fontysrobotics/cross_robot_localization_with_UWB_COLAB/PhysicalSystem/3D_Models/Downloaded/5mm-led-grommit-1.snapshot.1/5mm LED GROMMIT.jpg

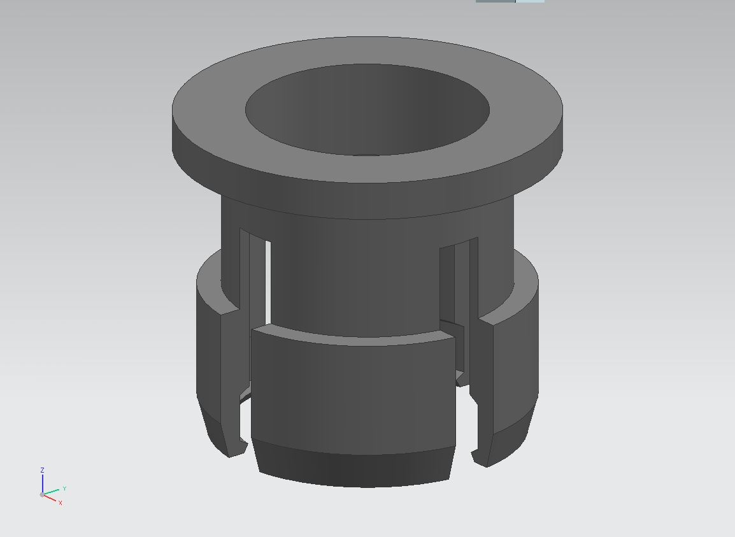
PhysicalSystem/3D_Models/Downloaded/5mm-led-grommit-1.snapshot.1/5mm LED GROMMIT.jpg
