fontysrobotics/cross_robot_localization_with_UWB_COLAB/PhysicalSystem/3D_Models/Downloaded/30mm-dc-fan-1.snapshot.6/30 fan decal.png

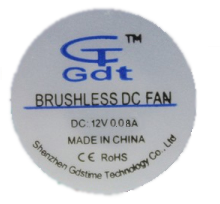
PhysicalSystem/3D_Models/Downloaded/30mm-dc-fan-1.snapshot.6/30 fan decal.png
