fontysrobotics/cross_robot_localization_with_UWB_COLAB/PhysicalSystem/3D_Models/Downloaded/30mm-dc-fan-1.snapshot.6/30mm fan.jpg

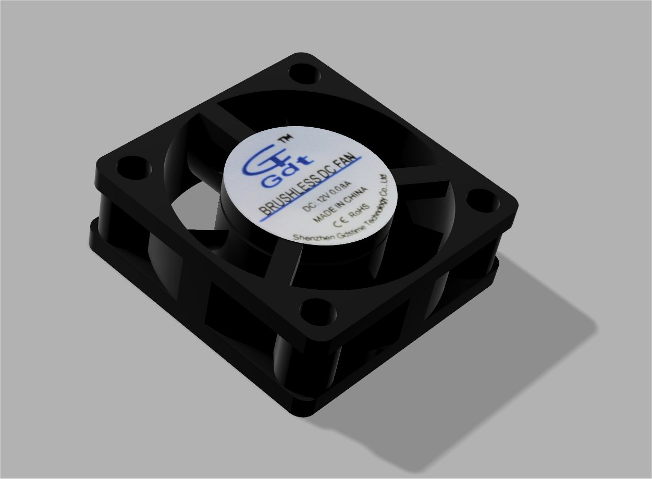
PhysicalSystem/3D_Models/Downloaded/30mm-dc-fan-1.snapshot.6/30mm fan.jpg
