fontysrobotics/cross_robot_localization_with_UWB_COLAB/PhysicalSystem/3D_Models/Downloaded/AAA battery holder/ScreenShot 2020-10-25 16.12.19.png

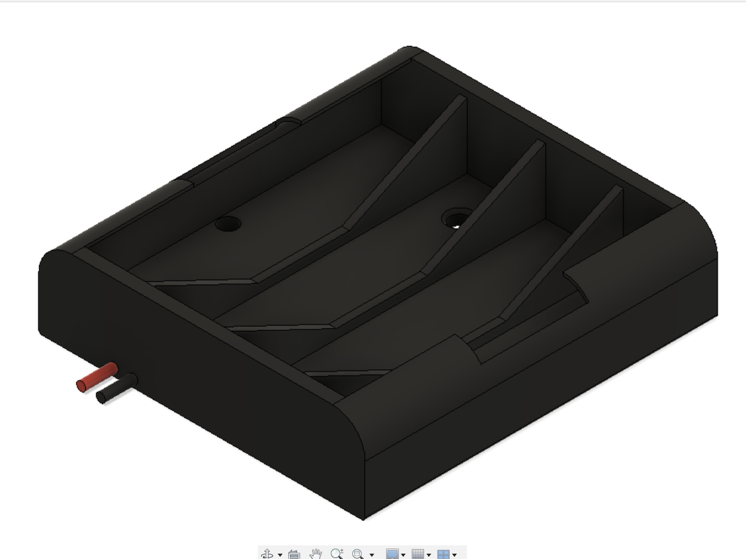
PhysicalSystem/3D_Models/Downloaded/AAA battery holder/ScreenShot 2020-10-25 16.12.19.png
