fontysrobotics/cross_robot_localization_with_UWB_COLAB/PhysicalSystem/3D_Models/Downloaded/led-5mm-2.snapshot.16/Renderings/untitled.57.jpg

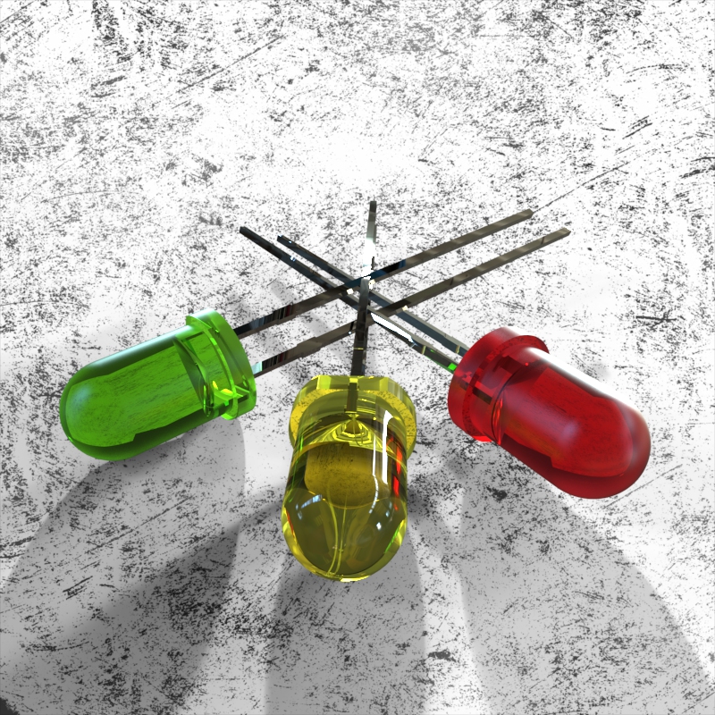
PhysicalSystem/3D_Models/Downloaded/led-5mm-2.snapshot.16/Renderings/untitled.57.jpg
