fontysrobotics/cross_robot_localization_with_UWB_COLAB/PhysicalSystem/3D_Models/Downloaded/m12-cable-gland-1.snapshot.1/gland_m12.jpg

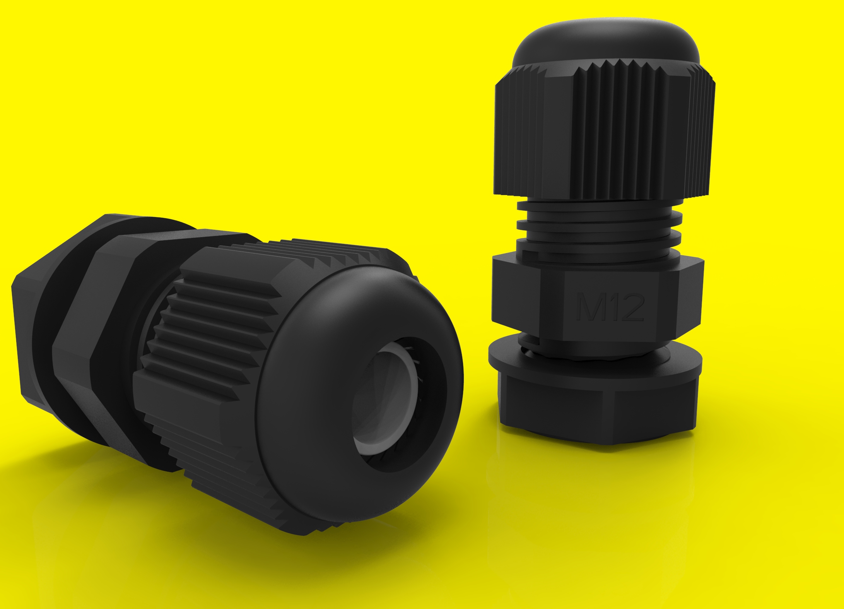
PhysicalSystem/3D_Models/Downloaded/m12-cable-gland-1.snapshot.1/gland_m12.jpg
