fontysrobotics/cross_robot_localization_with_UWB_COLAB/PhysicalSystem/3D_Models/Downloaded/small-power-switches-rocker-type-10-5x15mm-1.snapshot.7/KCD1-11-2P-Off.png

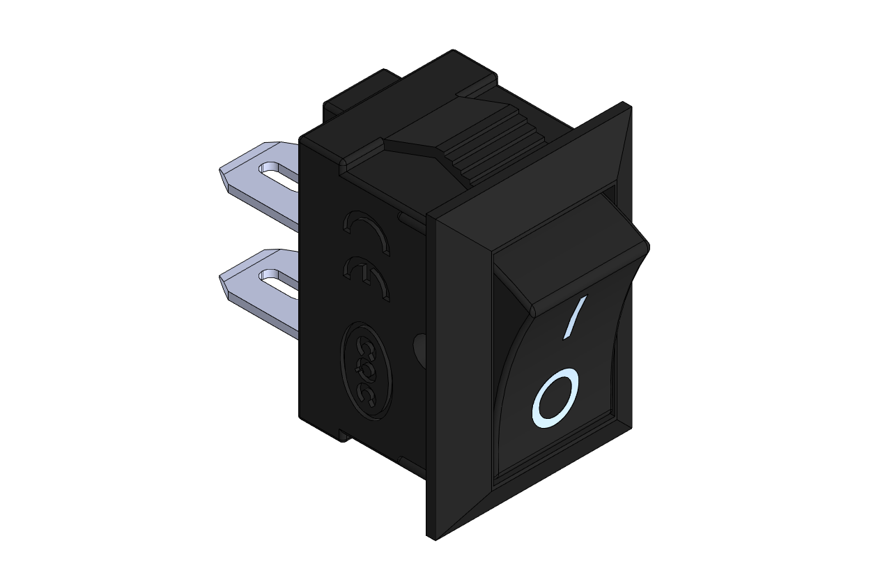
PhysicalSystem/3D_Models/Downloaded/small-power-switches-rocker-type-10-5x15mm-1.snapshot.7/KCD1-11-2P-Off.png
