fontysrobotics/cross_robot_localization_with_UWB_COLAB/Wiki_Images/AGVinfoAutonomy.PNG

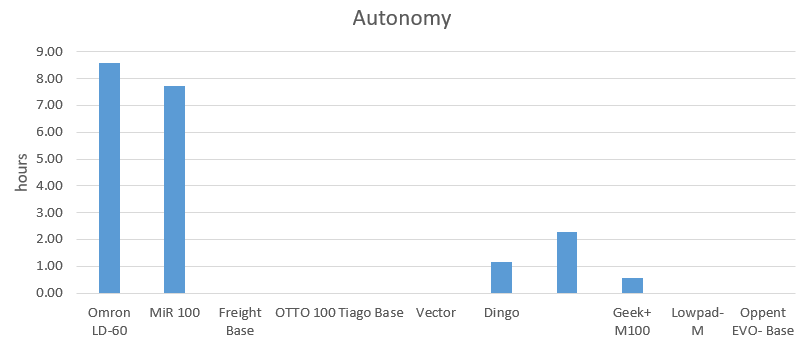
Wiki_Images/AGVinfoAutonomy.PNG
