fontysrobotics/cross_robot_localization_with_UWB_COLAB/Wiki_Images/AGVinfoBatteryTable.PNG

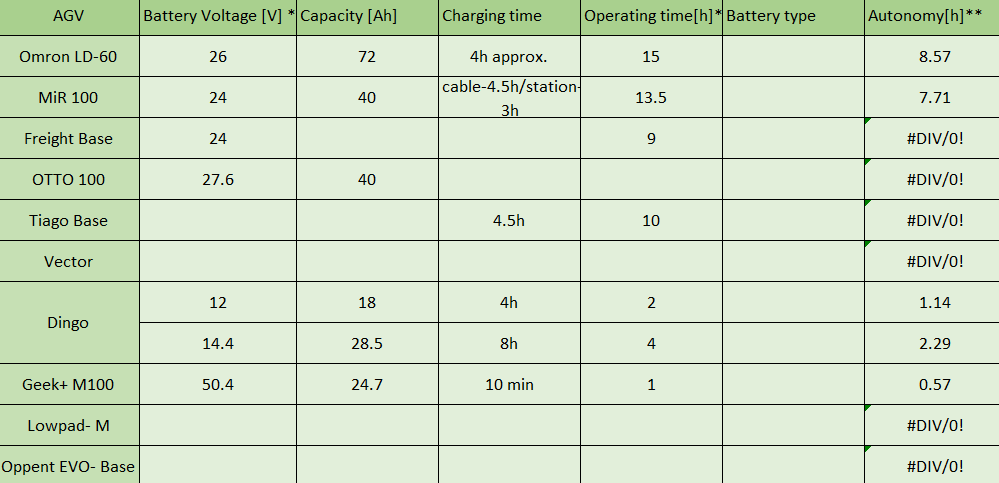
Wiki_Images/AGVinfoBatteryTable.PNG
