fontysrobotics/cross_robot_localization_with_UWB_COLAB/Wiki_Images/AGVinfoMaxLoad.PNG

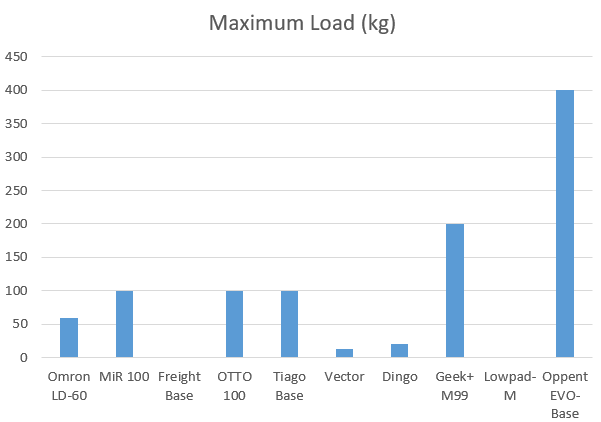
Wiki_Images/AGVinfoMaxLoad.PNG
