fontysrobotics/cross_robot_localization_with_UWB_COLAB/Wiki_Images/AGVinfoPlacement.PNG

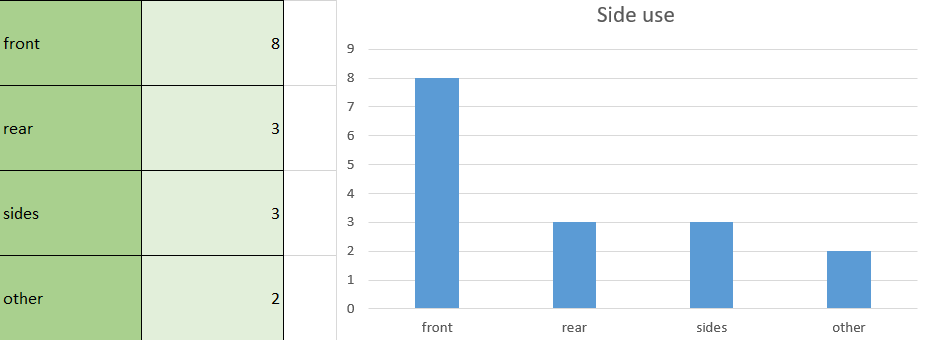
Wiki_Images/AGVinfoPlacement.PNG
