fontysrobotics/cross_robot_localization_with_UWB_COLAB/Wiki_Images/AGVinfoVolume.PNG

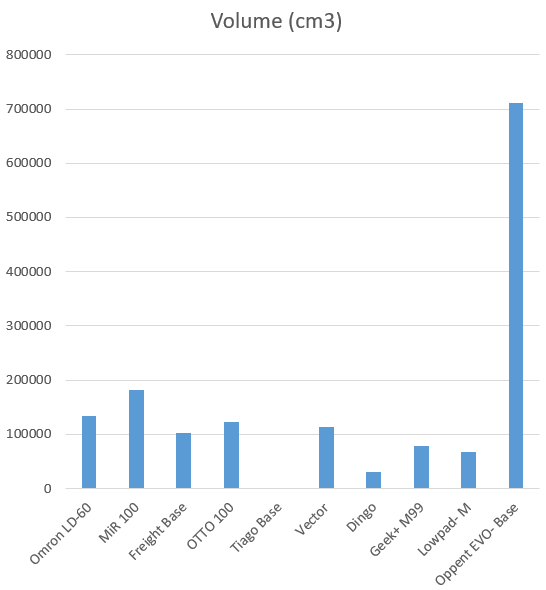
Wiki_Images/AGVinfoVolume.PNG
