fontysrobotics/cross_robot_localization_with_UWB_COLAB/Wiki_Images/AGVinfoWeight.PNG

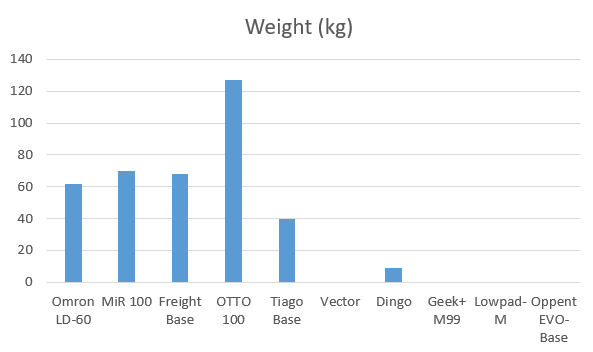
Wiki_Images/AGVinfoWeight.PNG
