fontysrobotics/cross_robot_localization_with_UWB_COLAB/Wiki_Images/CoLAB Housing PCB.png

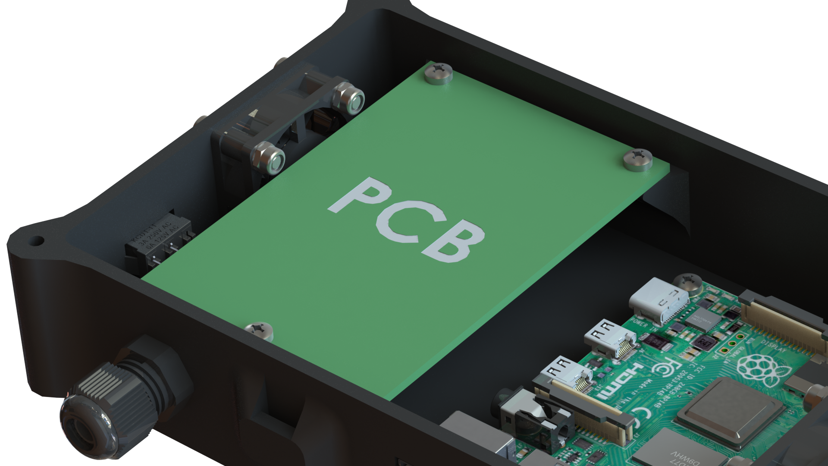
Wiki_Images/CoLAB Housing PCB.png
