fontysrobotics/cross_robot_localization_with_UWB_COLAB/Wiki_Images/CoLAB Housing Switch.png

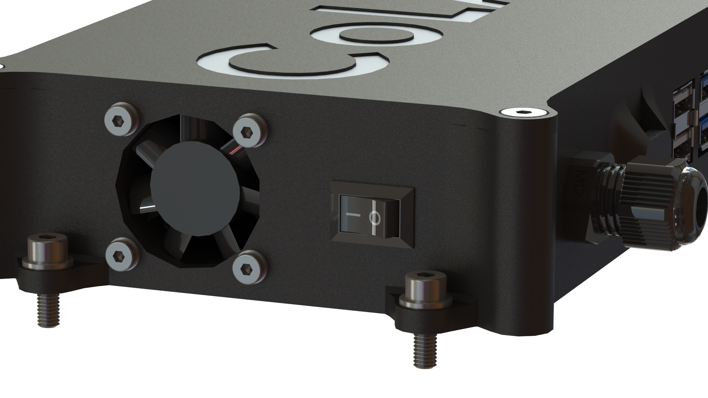
Wiki_Images/CoLAB Housing Switch.png
