fontysrobotics/cross_robot_localization_with_UWB_COLAB/Wiki_Images/connection_diagram_LM2596.JPG

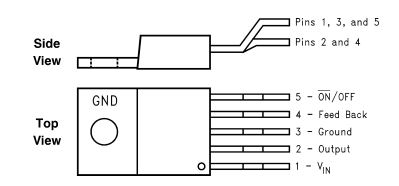
Wiki_Images/connection_diagram_LM2596.JPG
