fontysrobotics/cross_robot_localization_with_UWB_COLAB/Wiki_Images/DataProcessMidPoint.PNG

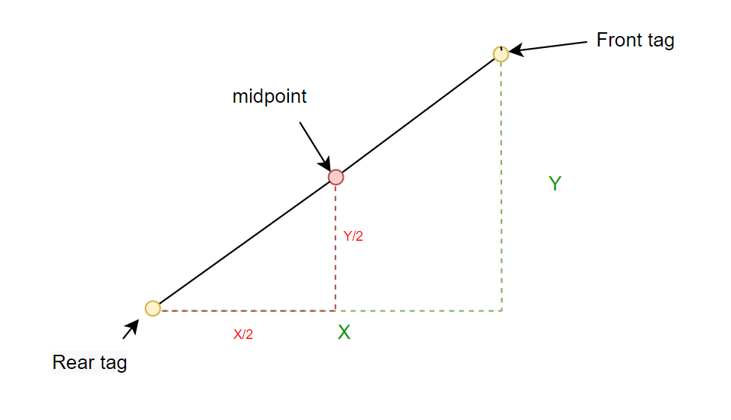
Wiki_Images/DataProcessMidPoint.PNG
