fontysrobotics/cross_robot_localization_with_UWB_COLAB/Wiki_Images/DRTLSmanager2.png

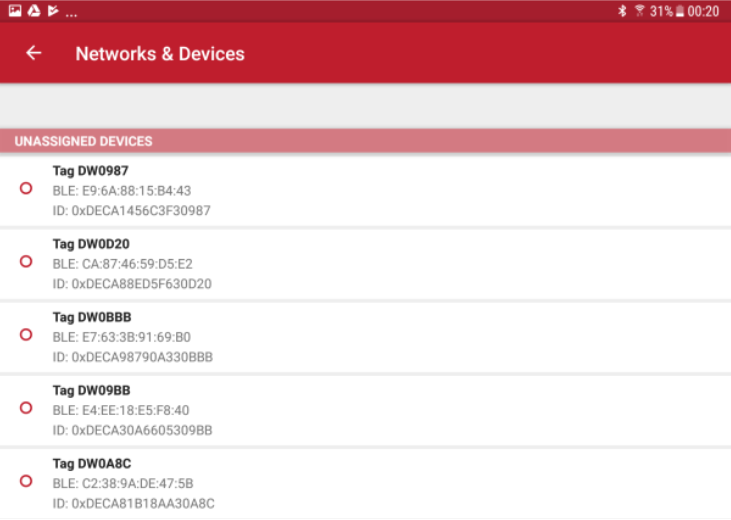
Wiki_Images/DRTLSmanager2.png
