fontysrobotics/cross_robot_localization_with_UWB_COLAB/Wiki_Images/HoldBot.PNG

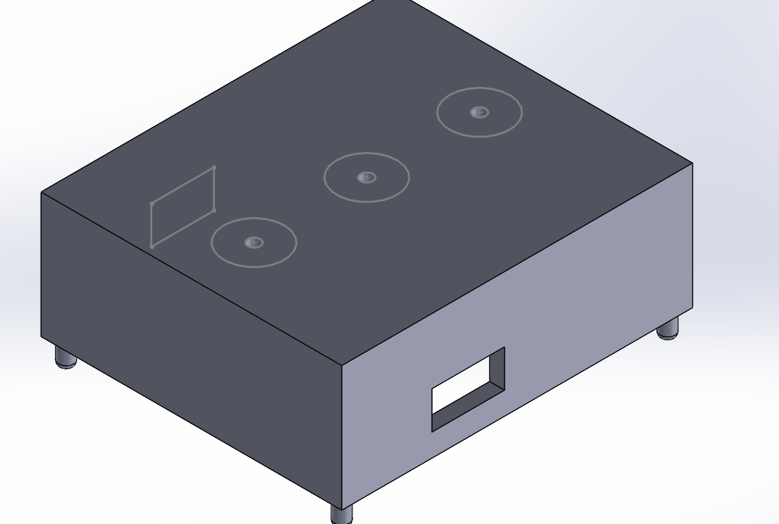
Wiki_Images/HoldBot.PNG
