fontysrobotics/cross_robot_localization_with_UWB_COLAB/Wiki_Images/LTC4060EFE_package.JPG

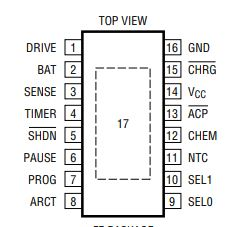
Wiki_Images/LTC4060EFE_package.JPG
