fontysrobotics/cross_robot_localization_with_UWB_COLAB/Wiki_Images/LTC4415_package.JPG

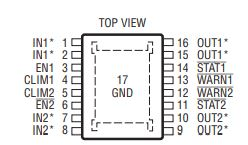
Wiki_Images/LTC4415_package.JPG
