fontysrobotics/cross_robot_localization_with_UWB_COLAB/Wiki_Images/MiR100_Application_interface.png

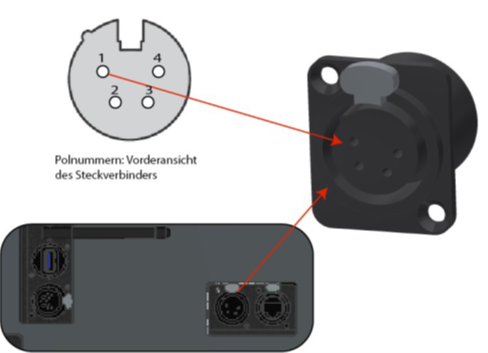
Wiki_Images/MiR100_Application_interface.png
