fontysrobotics/cross_robot_localization_with_UWB_COLAB/Wiki_Images/MiRTest2Cross2Tags.PNG

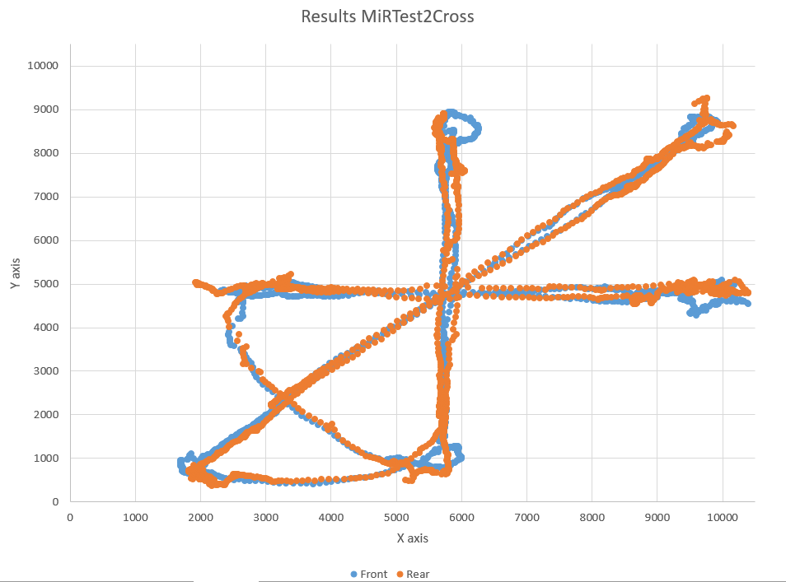
Wiki_Images/MiRTest2Cross2Tags.PNG
