fontysrobotics/cross_robot_localization_with_UWB_COLAB/Wiki_Images/MiRTest2CrossErrorZ.PNG

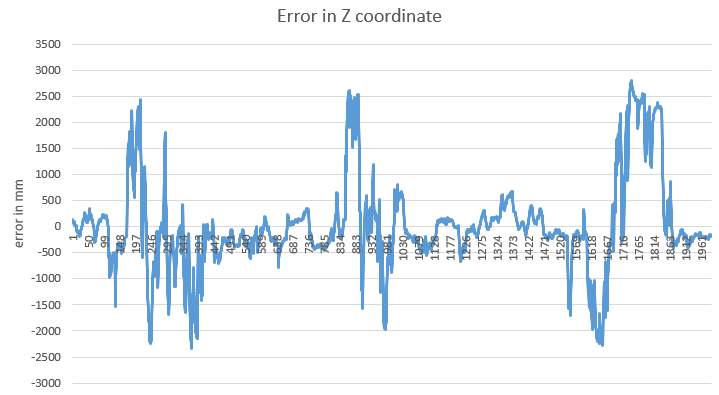
Wiki_Images/MiRTest2CrossErrorZ.PNG
