fontysrobotics/cross_robot_localization_with_UWB_COLAB/Wiki_Images/MiRTest2CrossMid.PNG

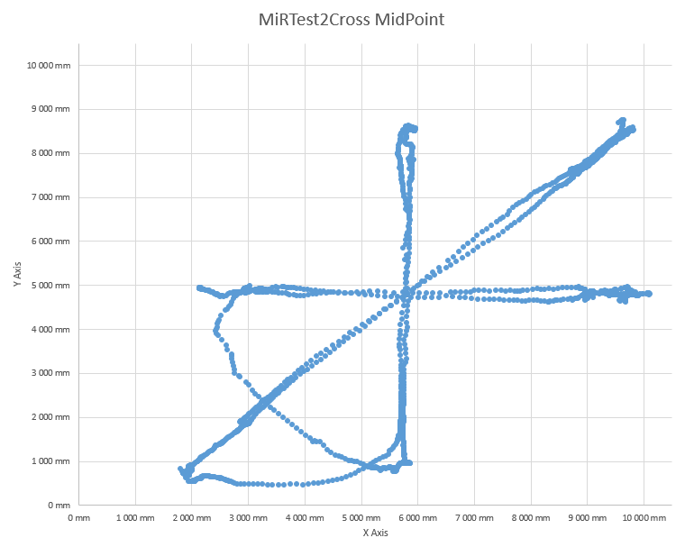
Wiki_Images/MiRTest2CrossMid.PNG
