fontysrobotics/cross_robot_localization_with_UWB_COLAB/Wiki_Images/pic 1.jpg

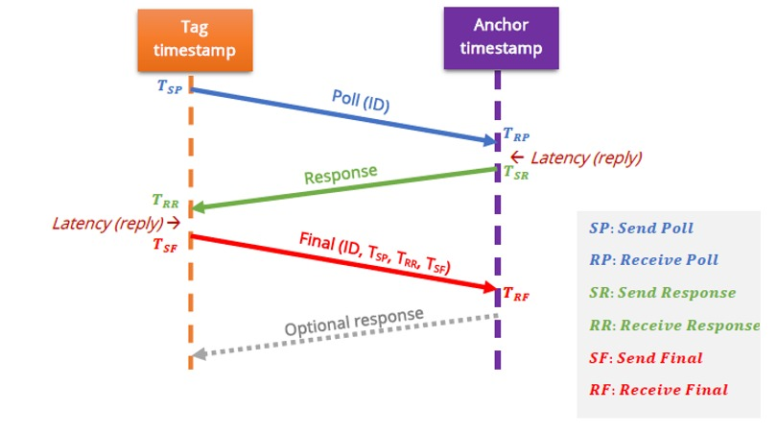
Wiki_Images/pic 1.jpg
