fontysrobotics/cross_robot_localization_with_UWB_COLAB/Wiki_Images/picture1.PNG

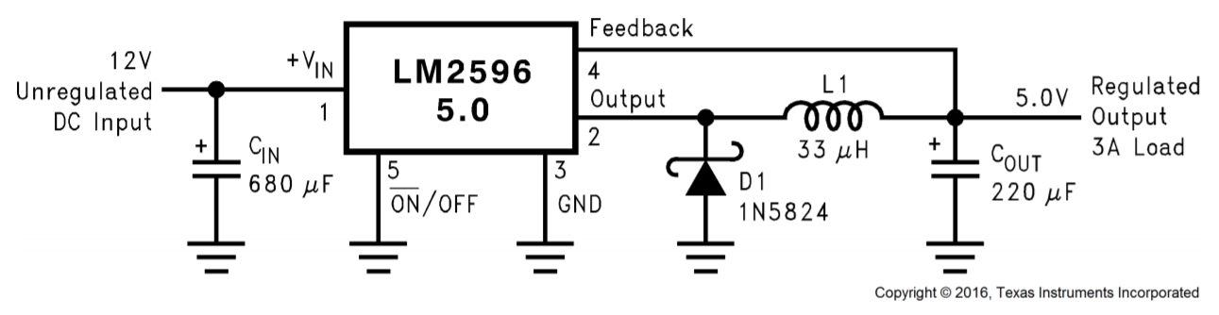
Wiki_Images/picture1.PNG
