fontysrobotics/cross_robot_localization_with_UWB_COLAB/Wiki_Images/picture2.PNG

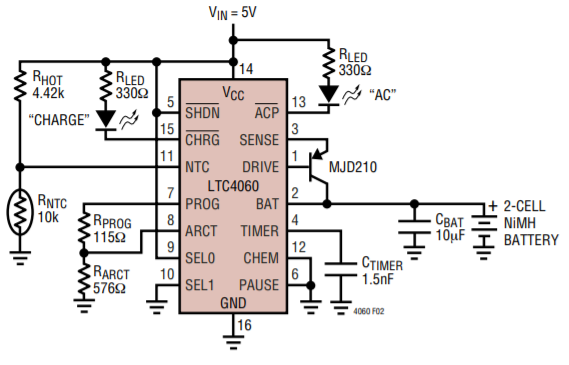
Wiki_Images/picture2.PNG
