fontysrobotics/cross_robot_localization_with_UWB_COLAB/Wiki_Images/picture3.PNG

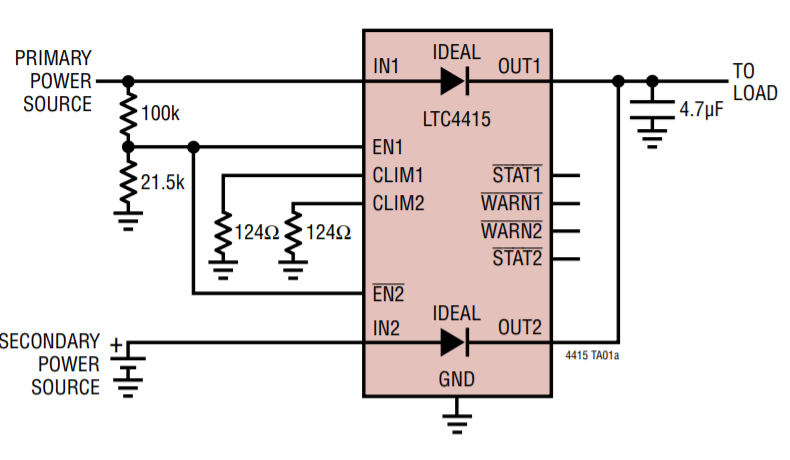
Wiki_Images/picture3.PNG
