fontysrobotics/cross_robot_localization_with_UWB_COLAB/Wiki_Images/UML class diagram CoLAB.png

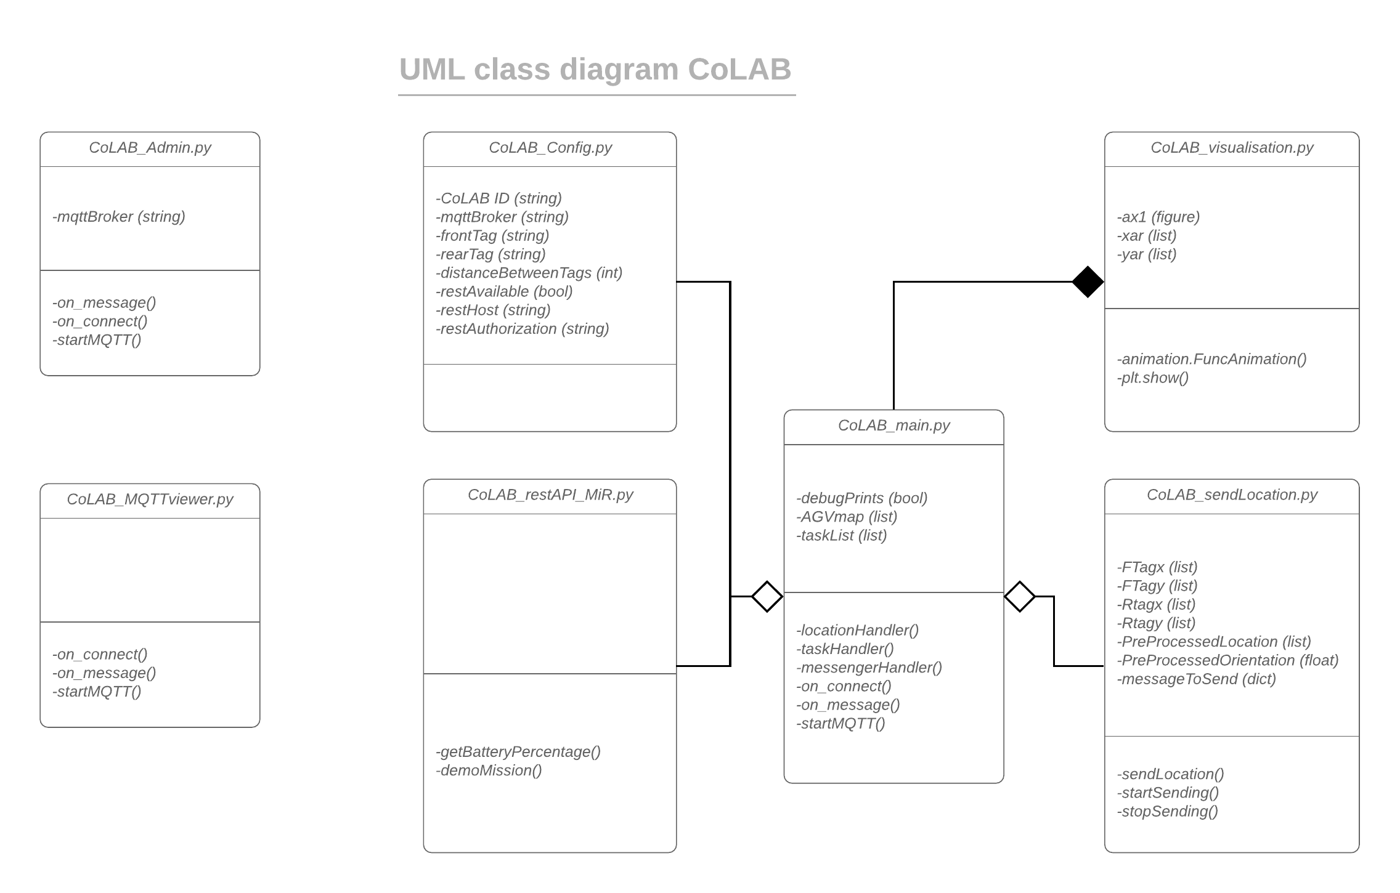
Wiki_Images/UML class diagram CoLAB.png
