fontysrobotics/cross_robot_localization_with_UWB_COLAB/Wiki_Images/UWBTestUWBNet.PNG

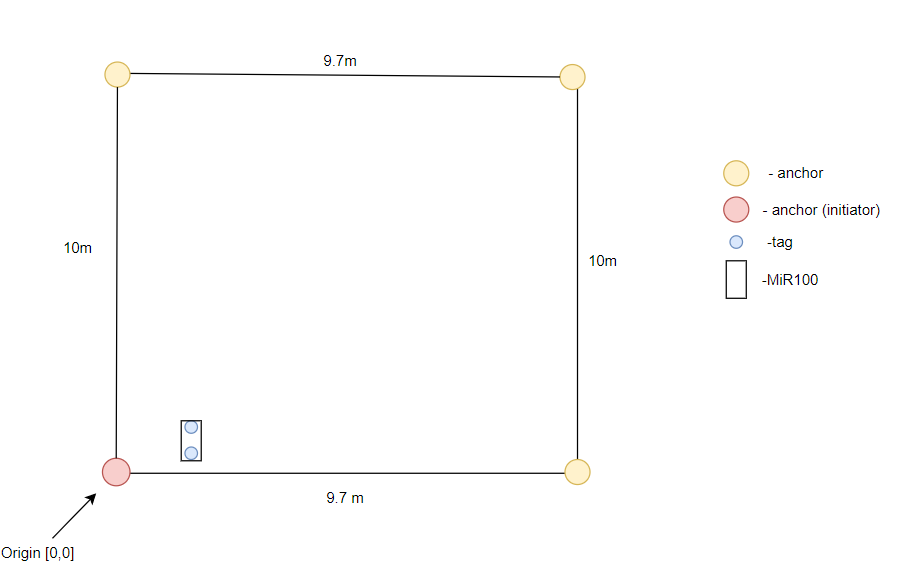
Wiki_Images/UWBTestUWBNet.PNG
