fontysrobotics/cross_robot_localization_with_UWB_COLAB/Wiki_Images/Visualisation.png

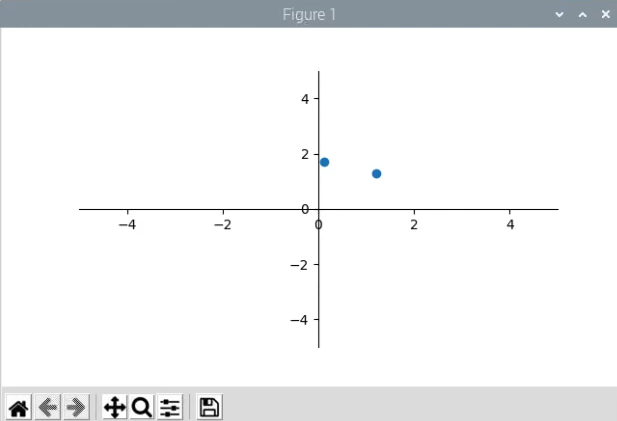
Wiki_Images/Visualisation.png
