fontysrobotics/cross_robot_localization_with_UWB_COLAB/Wiki_Images/WhatsApp Image 2021-01-27 at 12.03.13.jpeg

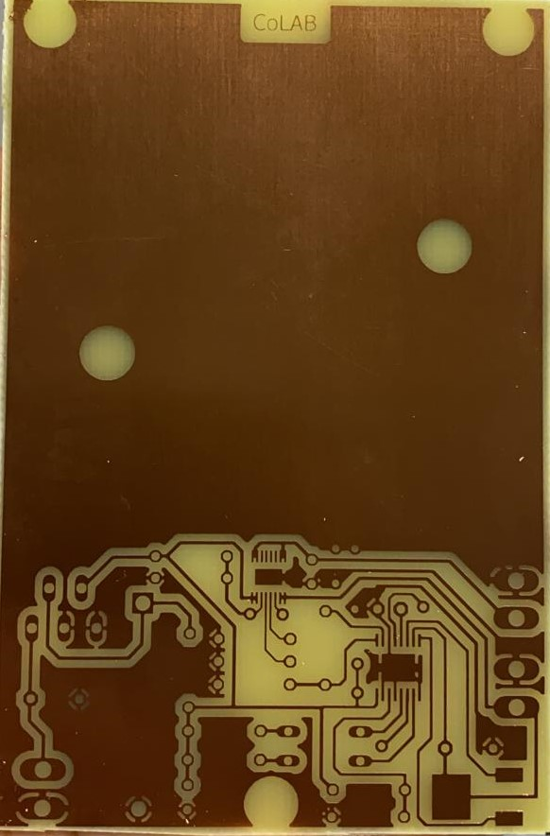
Wiki_Images/WhatsApp Image 2021-01-27 at 12.03.13.jpeg
