fontysrobotics/cross_robot_localization_with_UWB_COLAB/PhysicalSystem/Assembly_documents/Component _list_CoLAB.JPG

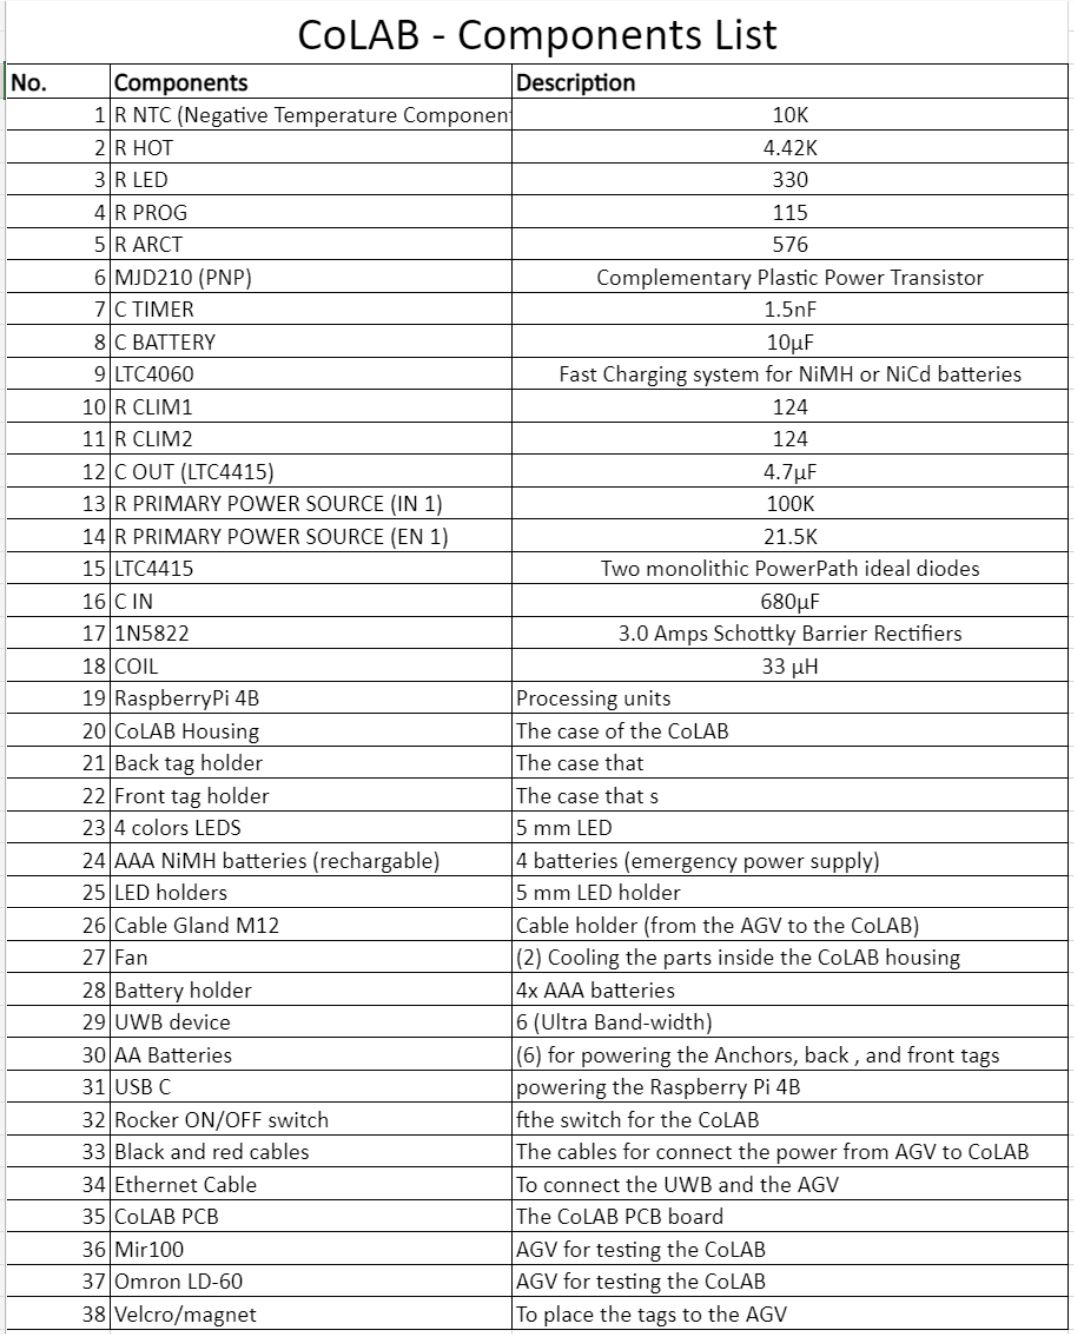
PhysicalSystem/Assembly_documents/Component _list_CoLAB.JPG
