fontysrobotics/cross_robot_localization_with_UWB_COLAB/Wiki_Images/MiR100_External_parts.png

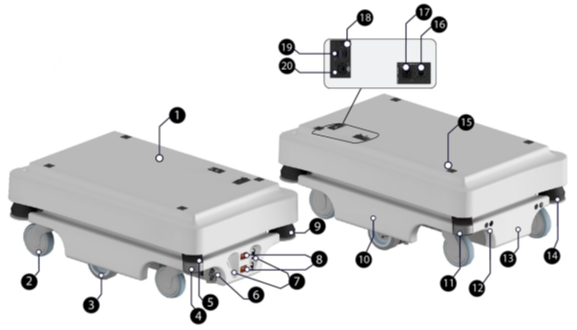
Wiki_Images/MiR100_External_parts.png
