fontysrobotics/cross_robot_localization_with_UWB_COLAB/PhysicalSystem/3D_Models/Tag_Holder/STLs/Tag Holder Top Part (1).STL

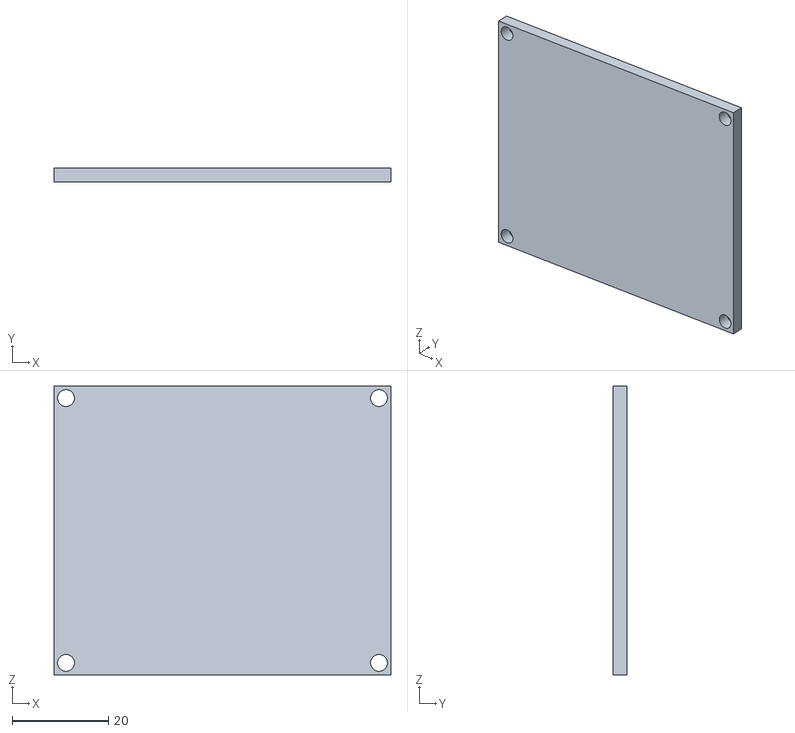
[picture p76: CAD file, 2021-02-01]
PhysicalSystem/3D_Models/Tag_Holder/STLs/Tag Holder Top Part (1).STL
70.0 x 3.00 x 60.0
