fontysrobotics/cross_robot_localization_with_UWB_COLAB/PhysicalSystem/3D_Models/CoLAB_Housing/CoLAB Case Top V2.SLDPRT

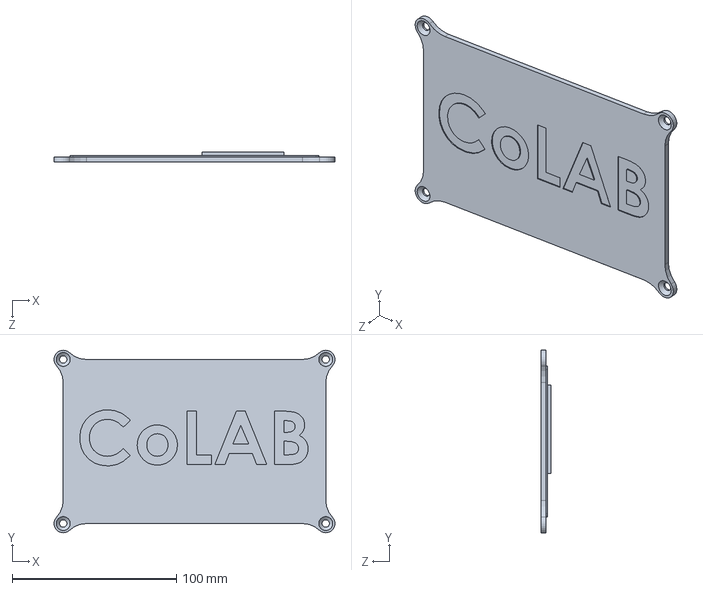
[picture p77: CAD file, 2021-01-27]
PhysicalSystem/3D_Models/CoLAB_Housing/CoLAB Case Top V2.SLDPRT
171.2 x 111.2 x 5.90 mm
