fontysrobotics/cross_robot_localization_with_UWB_COLAB/PhysicalSystem/3D_Models/Downloaded/raspberry-pi-4-model-b-1.snapshot.3/Display Connector, RPi4ModelB.SLDPRT

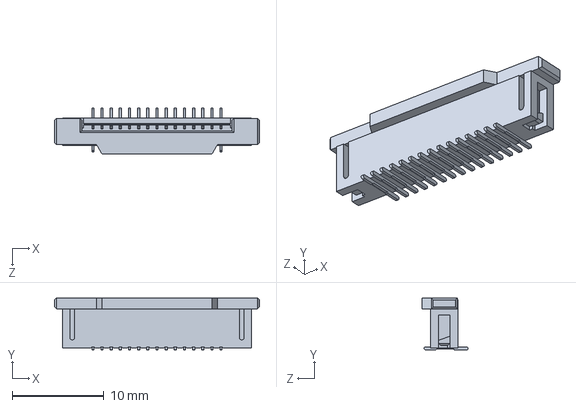
[picture p78: CAD file, 2021-01-27]
PhysicalSystem/3D_Models/Downloaded/raspberry-pi-4-model-b-1.snapshot.3/Display Connector, RPi4ModelB.SLDPRT
22.4 x 5.68 x 5.07 mm
