fontysrobotics/cross_robot_localization_with_UWB_COLAB/PhysicalSystem/3D_Models/CoLAB_Housing/CoLAB Case V2.SLDPRT

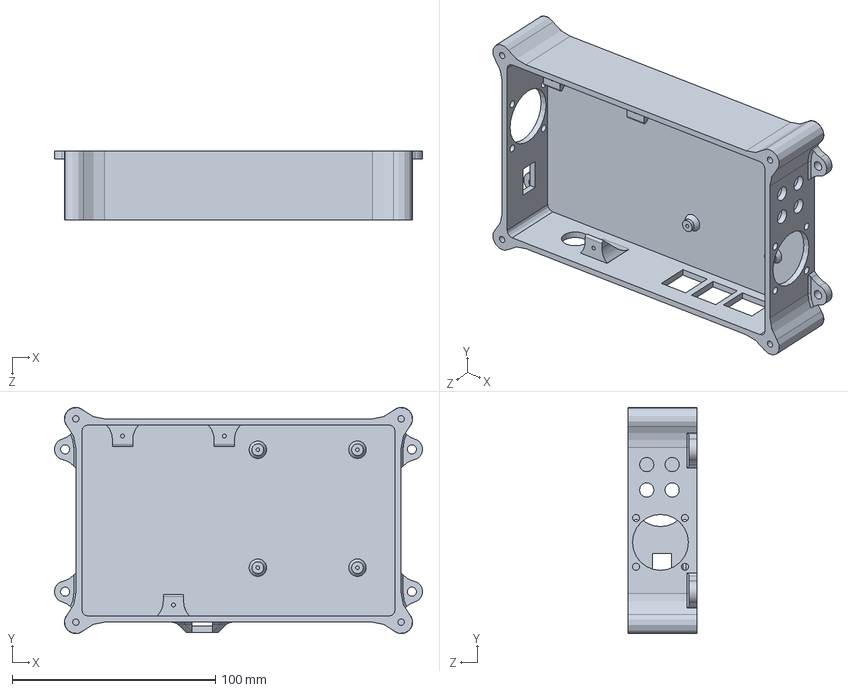
[picture p79: CAD file, 2021-01-27]
PhysicalSystem/3D_Models/CoLAB_Housing/CoLAB Case V2.SLDPRT
181.0 x 111.2 x 34.0 mm
