fontysrobotics/cross_robot_localization_with_UWB_COLAB/PhysicalSystem/3D_Models/Downloaded/raspberry-pi-4-model-b-1.snapshot.3/2X USB2.0 PORTS, RPi4ModelB.SLDPRT

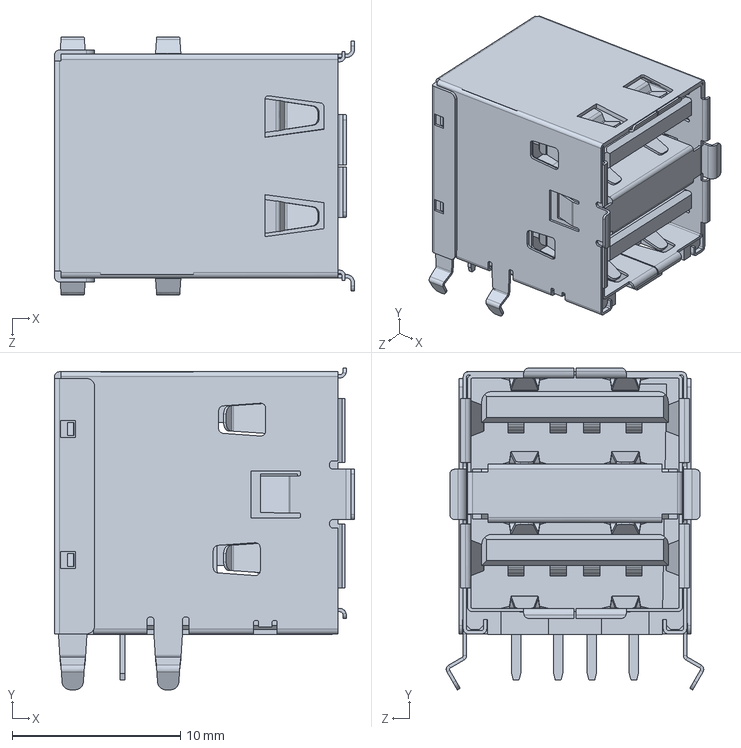
[picture p80: CAD file, 2021-01-27]
PhysicalSystem/3D_Models/Downloaded/raspberry-pi-4-model-b-1.snapshot.3/2X USB2.0 PORTS, RPi4ModelB.SLDPRT
17.9 x 19.2 x 15.3 mm
