fontysrobotics/cross_robot_localization_with_UWB_COLAB/PhysicalSystem/3D_Models/Downloaded/raspberry-pi-4-model-b-1.snapshot.3/2.54 mm DUPONT MALE PIN HEADER, IO, 2X20, RPi4ModelB.SLDPRT

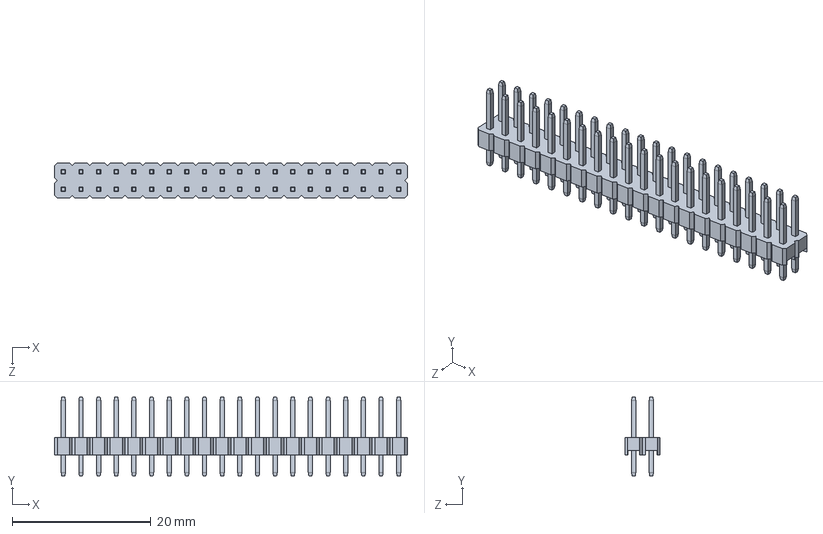
[picture p81: CAD file, 2021-01-27]
PhysicalSystem/3D_Models/Downloaded/raspberry-pi-4-model-b-1.snapshot.3/2.54 mm DUPONT MALE PIN HEADER, IO, 2X20, RPi4ModelB.SLDPRT
50.8 x 11.3 x 5.08 mm
