fontysrobotics/cross_robot_localization_with_UWB_COLAB/PhysicalSystem/3D_Models/Downloaded/raspberry-pi-4-model-b-1.snapshot.3/2X USB3.0 PORTS, RPi4ModelB.SLDPRT

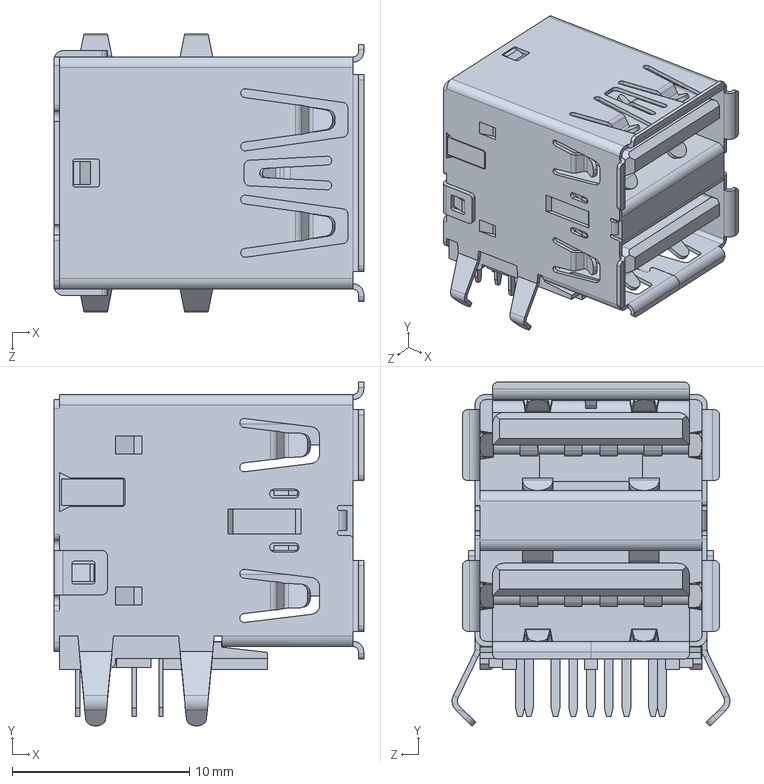
[picture p82: CAD file, 2021-01-27]
PhysicalSystem/3D_Models/Downloaded/raspberry-pi-4-model-b-1.snapshot.3/2X USB3.0 PORTS, RPi4ModelB.SLDPRT
17.5 x 19.4 x 15.7 mm
