fontysrobotics/cross_robot_localization_with_UWB_COLAB/PhysicalSystem/3D_Models/Downloaded/raspberry-pi-4-model-b-1.snapshot.3/Female Micro HDMI Connector, RPi4ModelB.SLDPRT

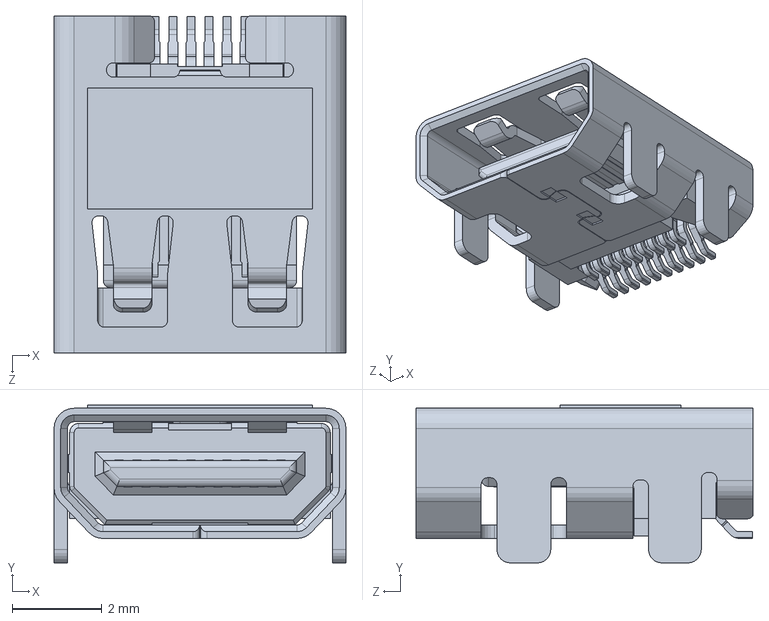
[picture p83: CAD file, 2021-01-27]
PhysicalSystem/3D_Models/Downloaded/raspberry-pi-4-model-b-1.snapshot.3/Female Micro HDMI Connector, RPi4ModelB.SLDPRT
6.50 x 3.52 x 7.50 mm
