fontysrobotics/cross_robot_localization_with_UWB_COLAB/PhysicalSystem/3D_Models/Downloaded/raspberry-pi-4-model-b-1.snapshot.3/91D77 D9WHV 778K, 4 GB LPDDR4 SDRAM, RPi4ModelB.SLDPRT

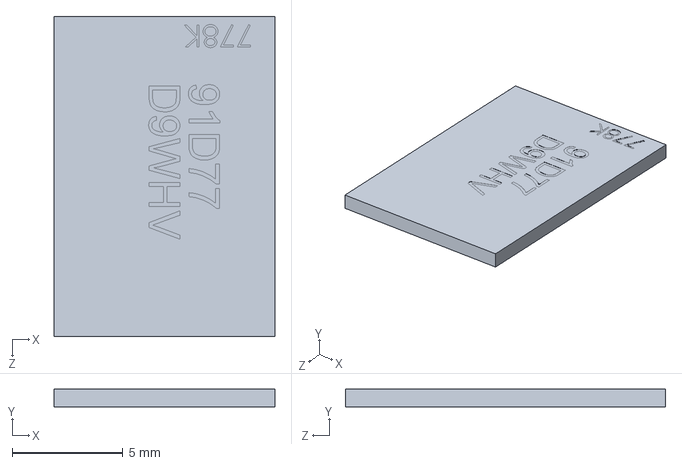
[picture p85: CAD file, 2021-01-27]
PhysicalSystem/3D_Models/Downloaded/raspberry-pi-4-model-b-1.snapshot.3/91D77 D9WHV 778K, 4 GB LPDDR4 SDRAM, RPi4ModelB.SLDPRT
10.0 x 0.8 x 14.5 mm
