fontysrobotics/cross_robot_localization_with_UWB_COLAB/PhysicalSystem/3D_Models/Downloaded/raspberry-pi-4-model-b-1.snapshot.3/Microphone Plug, RPi4ModelB.SLDPRT

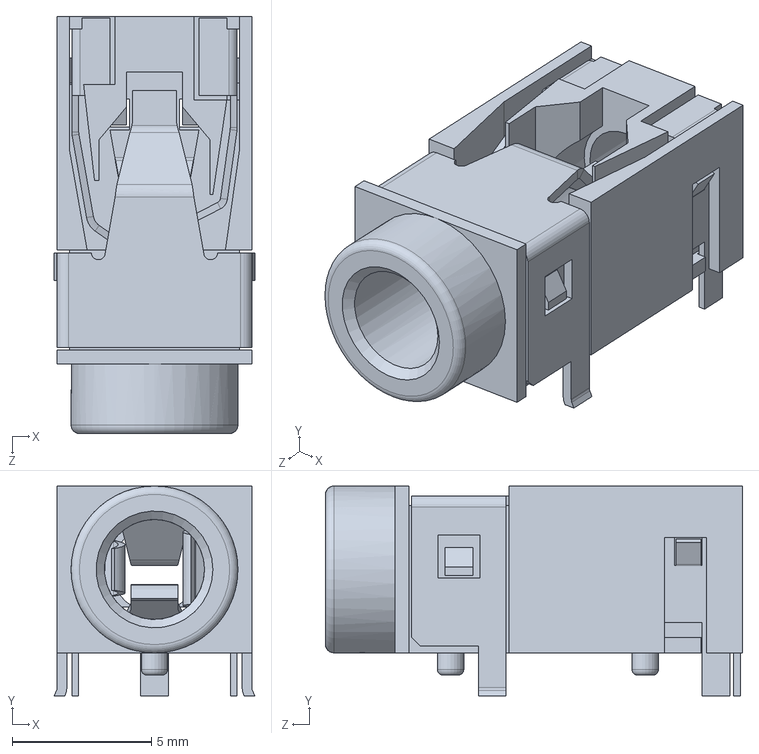
[picture p86: CAD file, 2021-01-27]
PhysicalSystem/3D_Models/Downloaded/raspberry-pi-4-model-b-1.snapshot.3/Microphone Plug, RPi4ModelB.SLDPRT
7.23 x 7.55 x 15.0 mm
