fontysrobotics/cross_robot_localization_with_UWB_COLAB/PhysicalSystem/3D_Models/Downloaded/raspberry-pi-4-model-b-1.snapshot.3/PCB, RPi4ModelB.SLDPRT

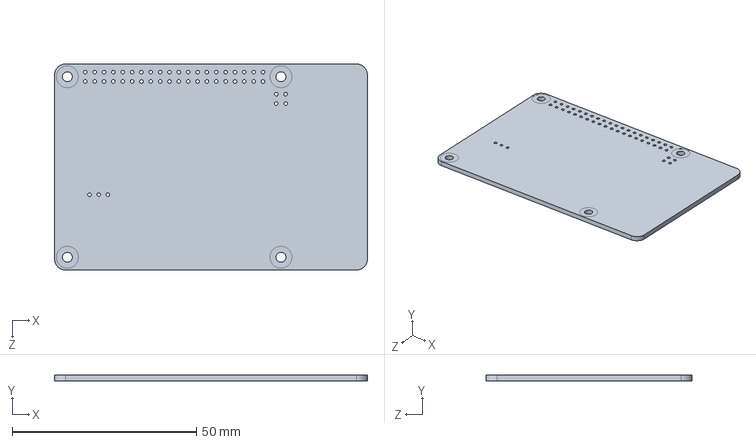
[picture p89: CAD file, 2021-01-27]
PhysicalSystem/3D_Models/Downloaded/raspberry-pi-4-model-b-1.snapshot.3/PCB, RPi4ModelB.SLDPRT
85.0 x 1.60 x 56.0 mm
