fontysrobotics/cross_robot_localization_with_UWB_COLAB/PhysicalSystem/3D_Models/Downloaded/raspberry-pi-4-model-b-1.snapshot.3/Broadcom BCM2711B0 CPU, RPi4ModelB.SLDPRT

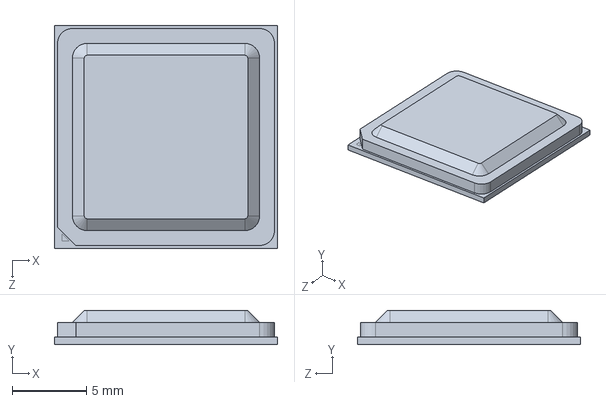
[picture p90: CAD file, 2021-01-27]
PhysicalSystem/3D_Models/Downloaded/raspberry-pi-4-model-b-1.snapshot.3/Broadcom BCM2711B0 CPU, RPi4ModelB.SLDPRT
15.0 x 2.30 x 15.0 mm
