fontysrobotics/cross_robot_localization_with_UWB_COLAB/PhysicalSystem/3D_Models/Downloaded/raspberry-pi-4-model-b-1.snapshot.3/Gigabit Ethernet Port, RPi4ModelB.SLDPRT

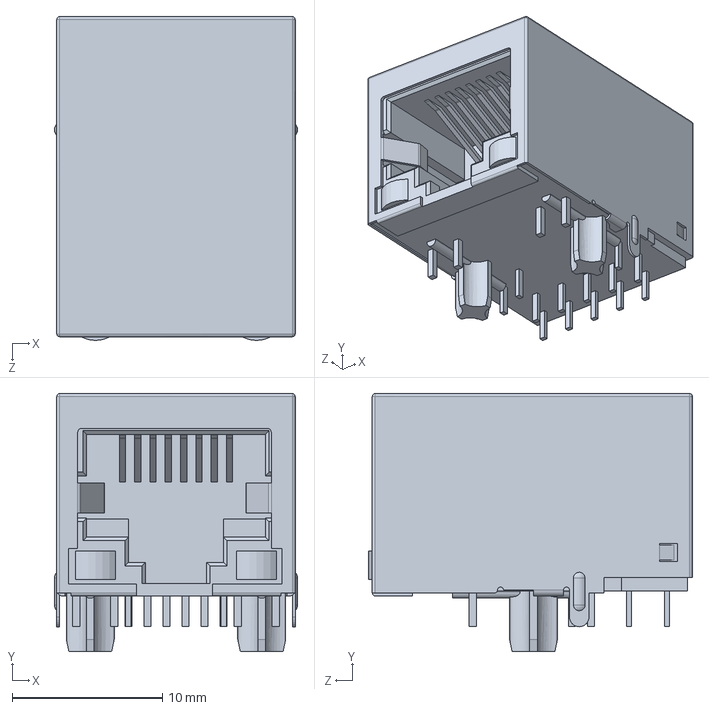
[picture p92: CAD file, 2021-01-27]
PhysicalSystem/3D_Models/Downloaded/raspberry-pi-4-model-b-1.snapshot.3/Gigabit Ethernet Port, RPi4ModelB.SLDPRT
16.2 x 17.2 x 21.6 mm
