fontysrobotics/cross_robot_localization_with_UWB_COLAB/AGV_information/User_Manual_Omron/Images/omron layout.jpg

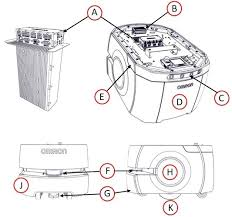
AGV_information/User_Manual_Omron/Images/omron layout.jpg
