fontysrobotics/cross_robot_localization_with_UWB_COLAB/Wiki_Images/constructangledistance.gif

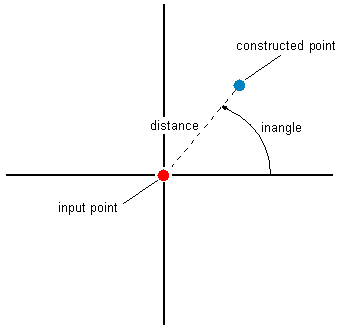
Wiki_Images/constructangledistance.gif
